DustinGrau/PinewoodLaneIndicator/Photos/IMG_6668.jpg

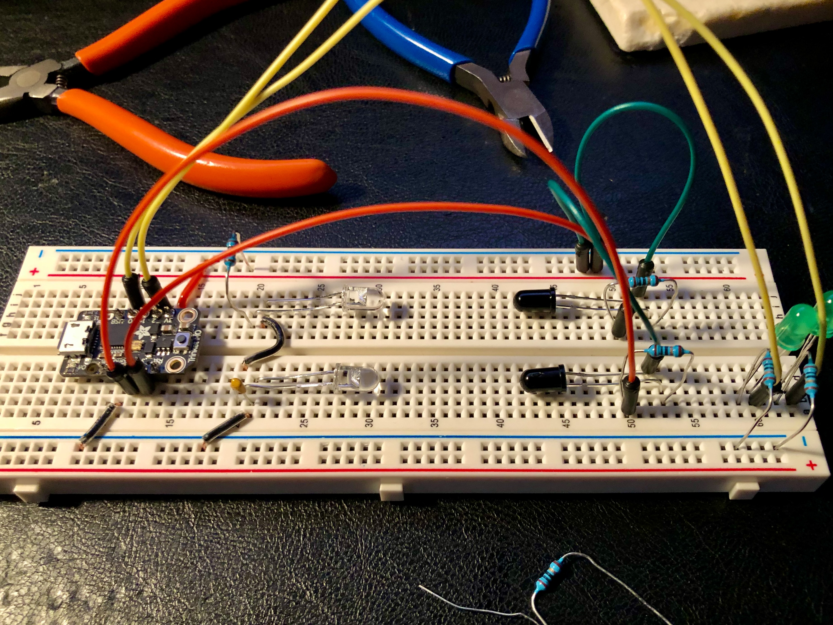
Photos/IMG_6668.jpg
