DustinGrau/PinewoodLaneIndicator/Photos/IMG_6680.jpg

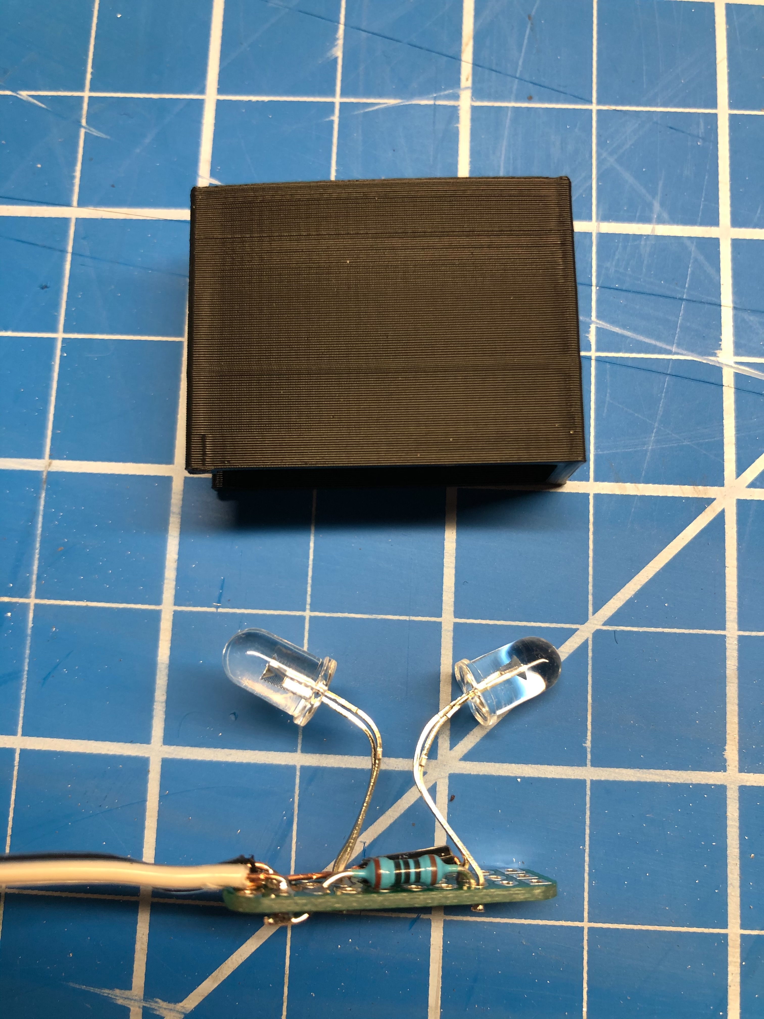
Photos/IMG_6680.jpg
