DustinGrau/PinewoodLaneIndicator/Photos/IMG_6681.jpg

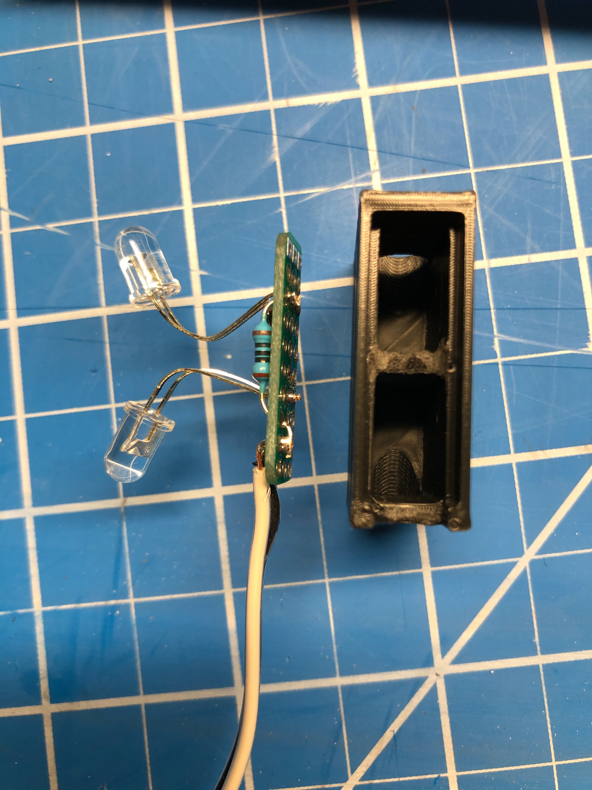
Photos/IMG_6681.jpg
