DustinGrau/PinewoodLaneIndicator/Photos/IMG_6684.jpg

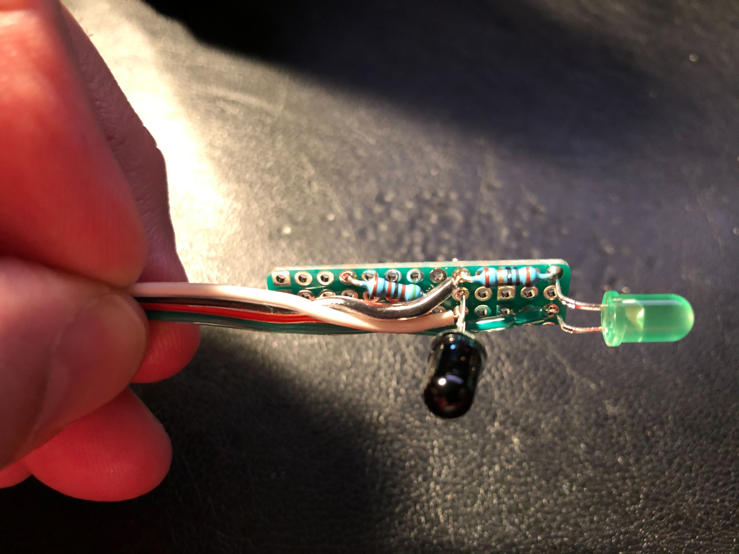
Photos/IMG_6684.jpg
