DustinGrau/PinewoodLaneIndicator/Photos/IMG_6685.jpg

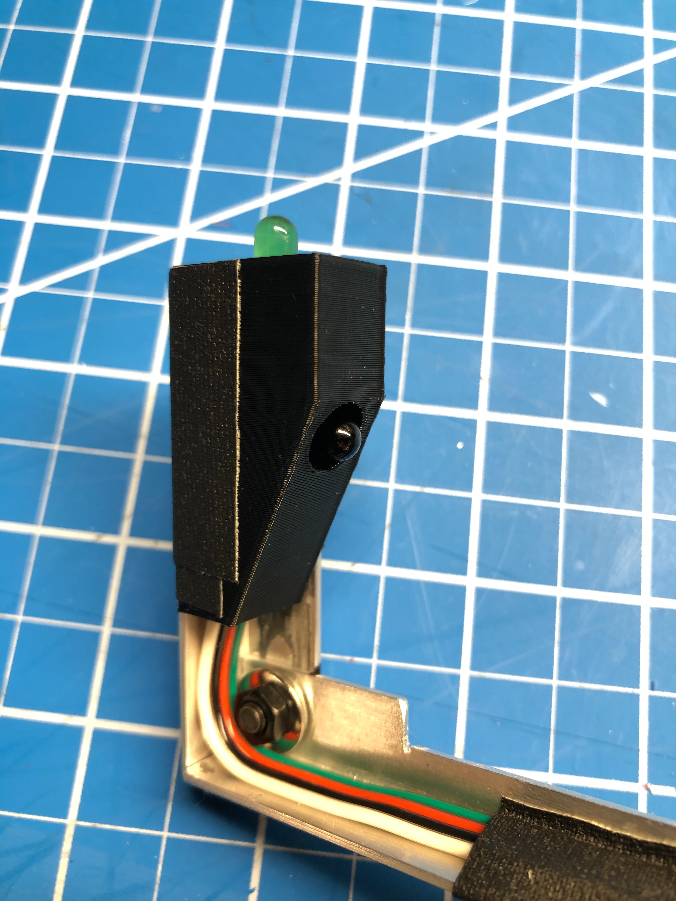
Photos/IMG_6685.jpg
