DustinGrau/PinewoodLaneIndicator/Photos/IMG_6688.jpg

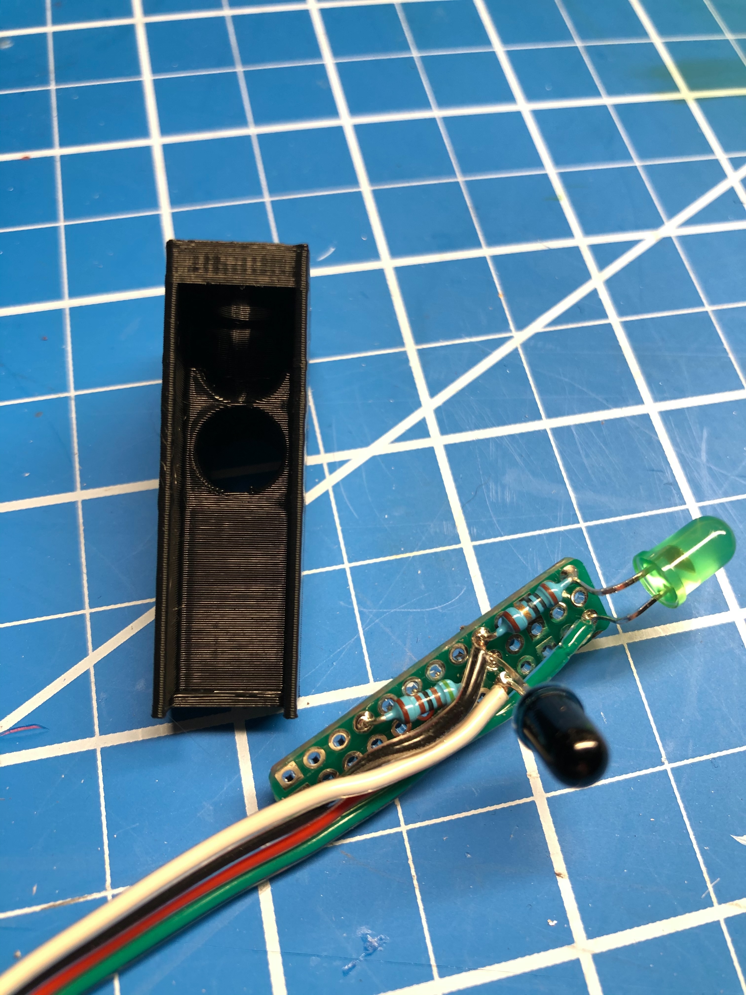
Photos/IMG_6688.jpg
