DustinGrau/PinewoodLaneIndicator/Photos/IMG_6697.jpg

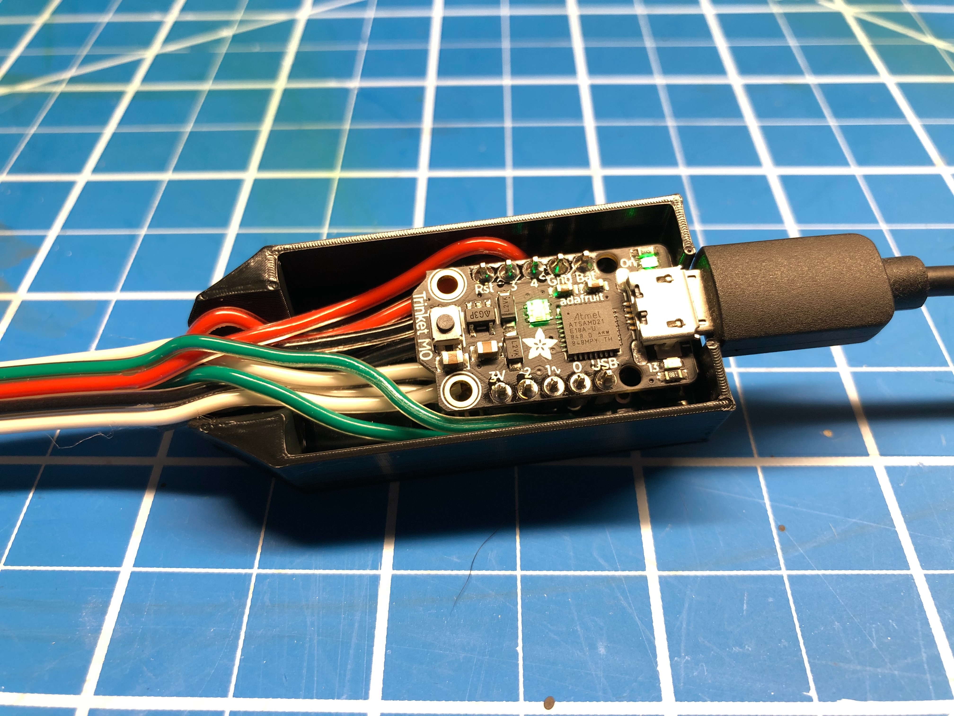
Photos/IMG_6697.jpg
