DustinGrau/PinewoodLaneIndicator/Photos/IMG_6700.jpg

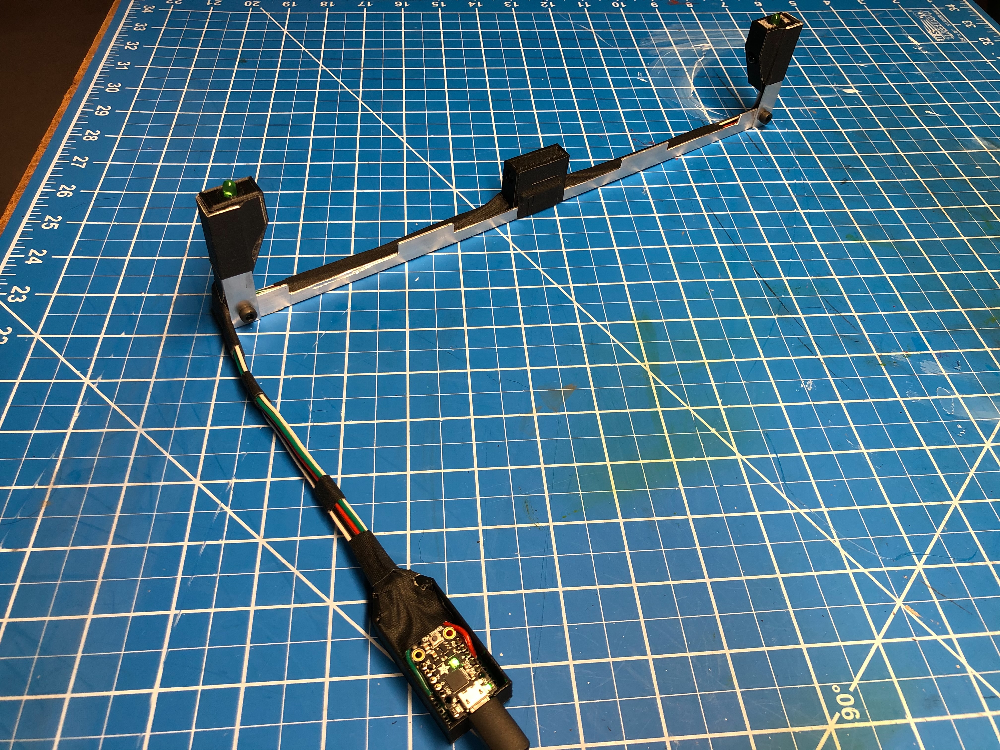
Photos/IMG_6700.jpg
