DustinGrau/PinewoodLaneIndicator/Photos/IMG_6724.jpg

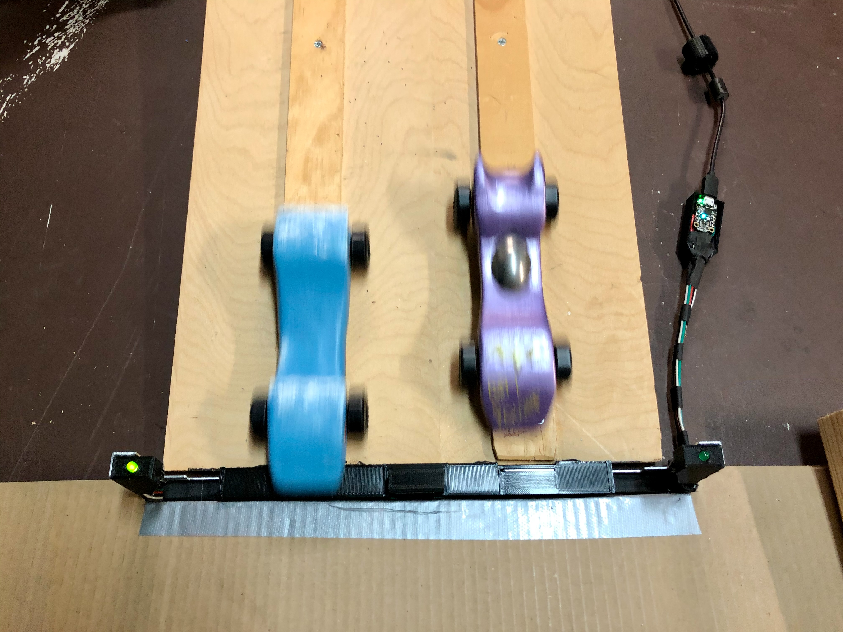
Photos/IMG_6724.jpg
